e3donline/ToolChanger/Revo Hemera XS Direct Tool/Mirrored Tool/STPs/Blower fan duct (M).STEP

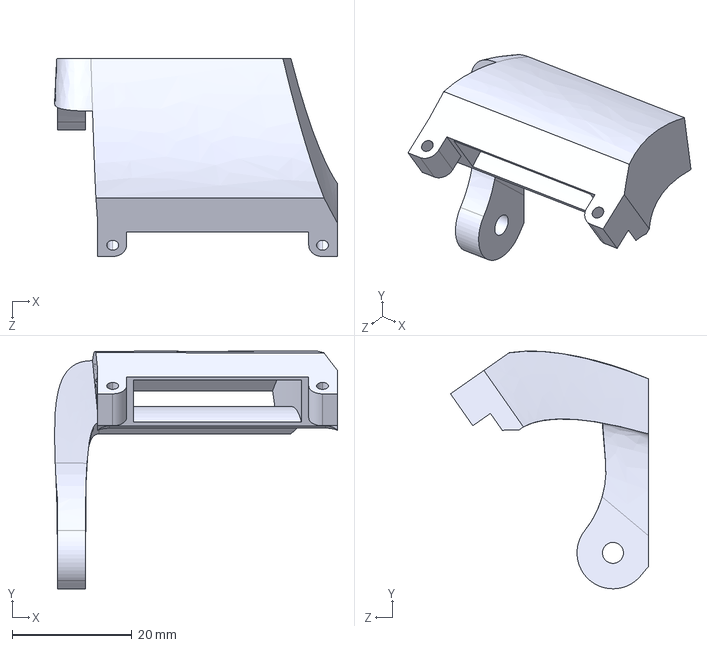
[picture p16: CAD file, 2023-03-06]
Revo Hemera XS Direct Tool/Mirrored Tool/STPs/Blower fan duct (M).STEP
47.2 x 39.6 x 33.0 mm
