e3donline/ToolChanger/Revo Hemera XS Direct Tool/Regular Tool/STPs/Dock brace.STEP

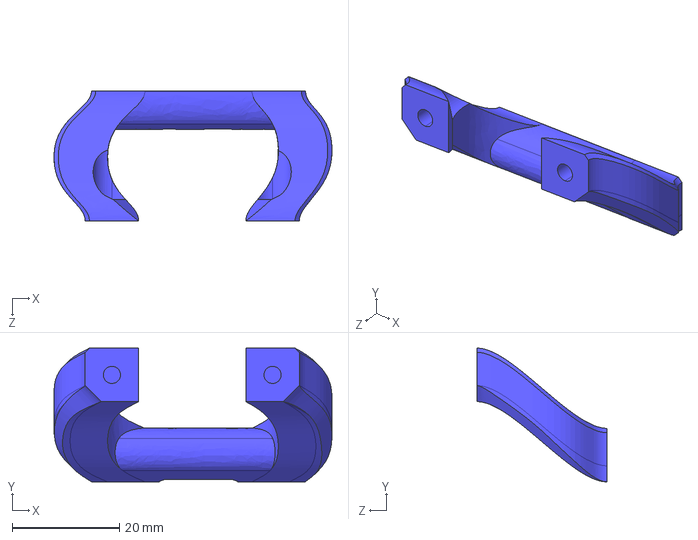
[picture p17: CAD file, 2023-03-06]
Revo Hemera XS Direct Tool/Regular Tool/STPs/Dock brace.STEP
51.9 x 25.0 x 24.3 mm
