e3donline/ToolChanger/STLs/Tool-Changer Cover Dot.stl

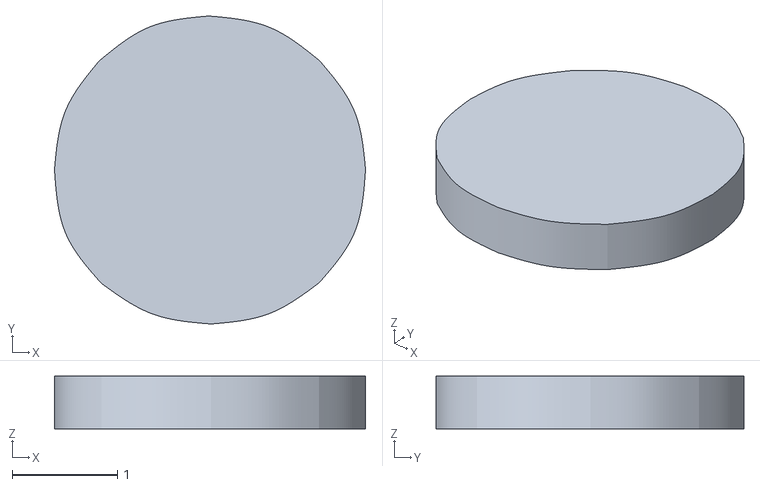
[picture p18: CAD file, 2019-06-24]
STLs/Tool-Changer Cover Dot.stl
2.95 x 2.92 x 0.5
