e3donline/ToolChanger/STPs/Tool-Changer Cover.step

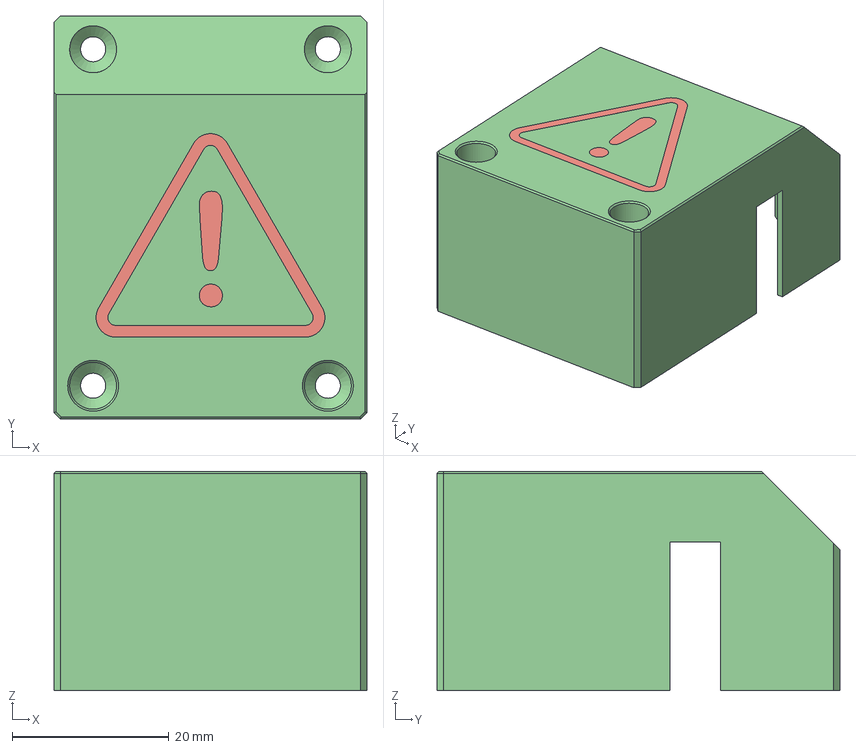
[picture p19: CAD file, 2019-07-31]
STPs/Tool-Changer Cover.step
40.0 x 51.5 x 28.0 mm
