e3donline/ToolChanger/Hemera Direct Tool/STPs/TC-DOCK-V6-DOCK-ADAPTER.step

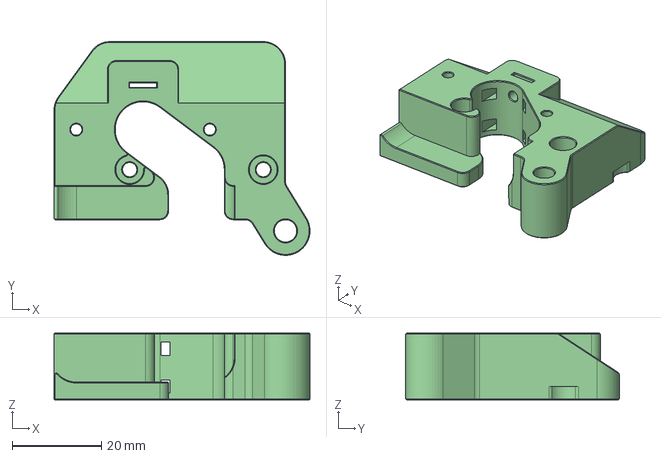
[picture p20: CAD file, 2021-03-15]
Hemera Direct Tool/STPs/TC-DOCK-V6-DOCK-ADAPTER.step
57.5 x 48.0 x 15.0 mm
