e3donline/ToolChanger/Revo Hemera XS Direct Tool/Regular Tool/STPs/Blower fan duct.STEP

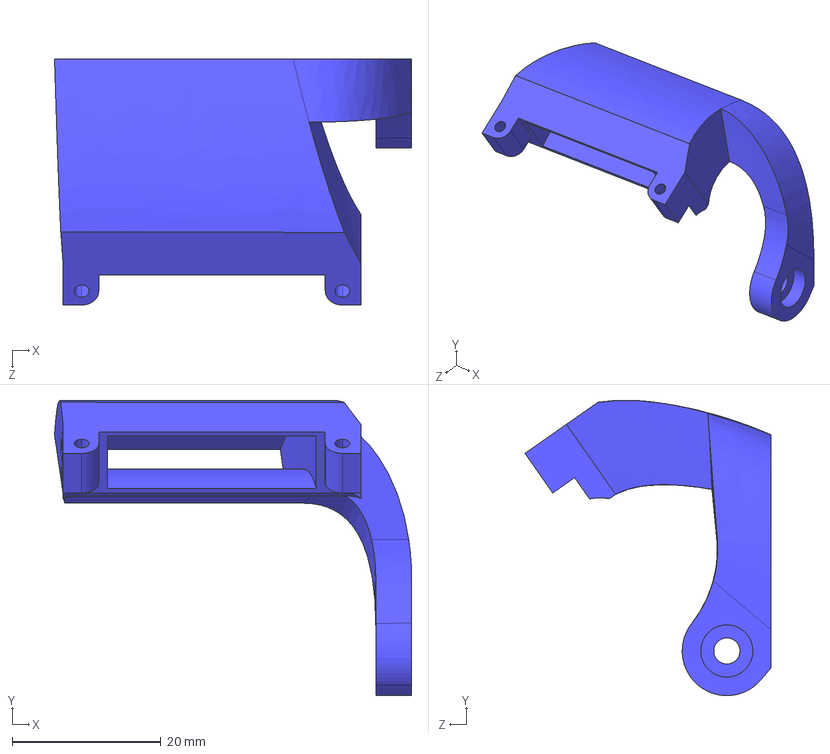
[picture p21: CAD file, 2023-03-06]
Revo Hemera XS Direct Tool/Regular Tool/STPs/Blower fan duct.STEP
47.9 x 39.6 x 33.0 mm
