e3donline/ToolChanger/STLs/X-Carriage Cables.stl

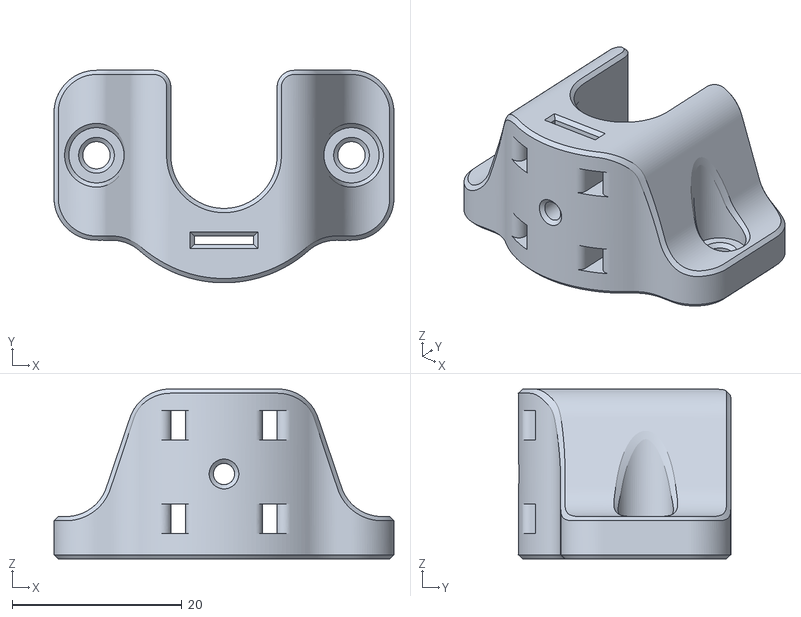
[picture p22: CAD file, 2019-06-24]
STLs/X-Carriage Cables.stl
40.0 x 25.0 x 20.0
