e3donline/ToolChanger/V6 Tool/STPs/V6 PCF Duct.step

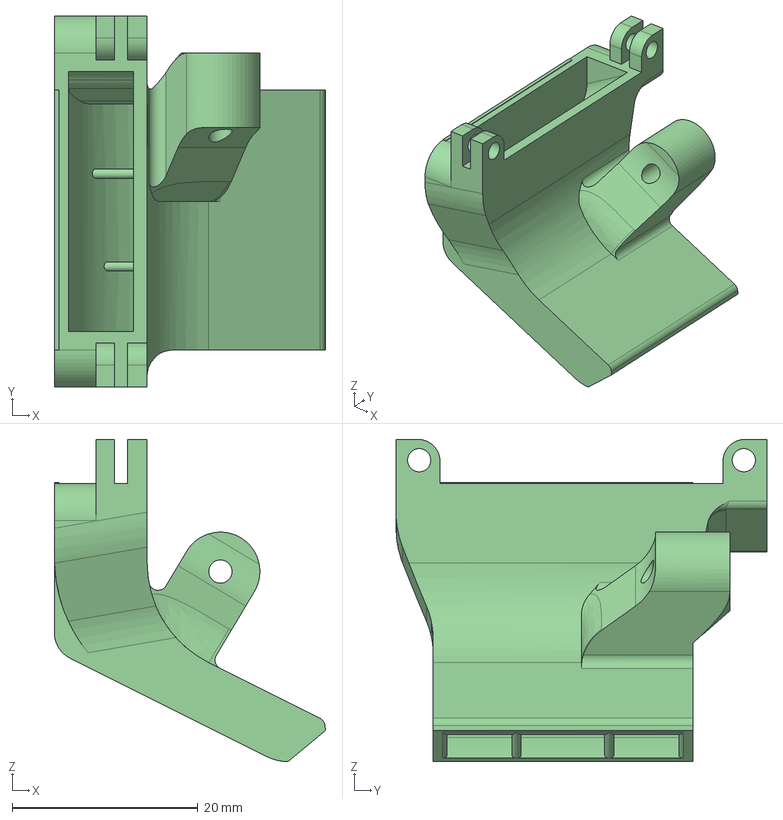
[picture p23: CAD file, 2019-07-31]
V6 Tool/STPs/V6 PCF Duct.step
29.2 x 40.0 x 34.8 mm
