e3donline/ToolChanger/Hemera Direct Tool/STPs/TC-V6-HEMERA-DOCK-BRACE-V2.step

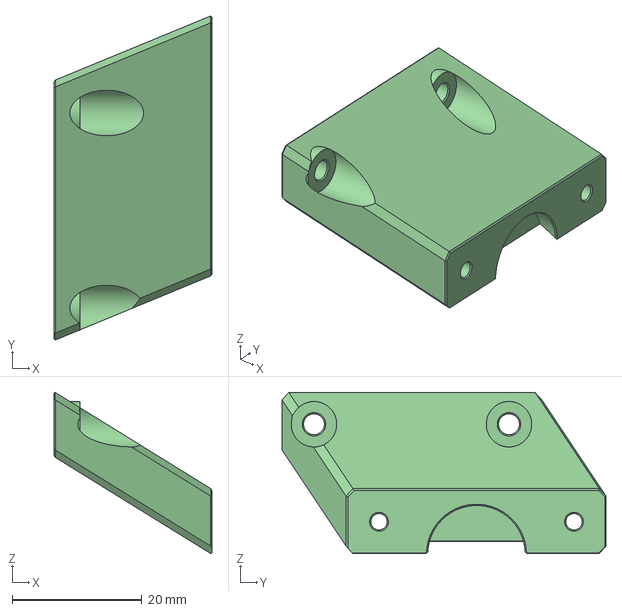
[picture p24: CAD file, 2021-03-15]
Hemera Direct Tool/STPs/TC-V6-HEMERA-DOCK-BRACE-V2.step
24.2 x 49.8 x 24.8 mm
