e3donline/ToolChanger/Revo Hemera XS Direct Tool/Mirrored Tool/STPs/Dock to RHXS (M).STEP

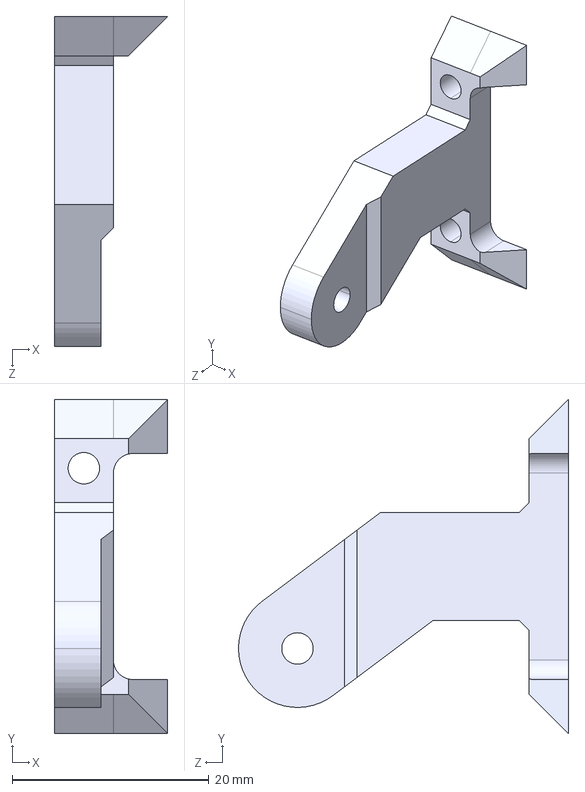
[picture p25: CAD file, 2023-03-06]
Revo Hemera XS Direct Tool/Mirrored Tool/STPs/Dock to RHXS (M).STEP
11.5 x 34.0 x 33.6 mm
