e3donline/ToolChanger/STLs/Tool-Changer Cover Triangle.stl

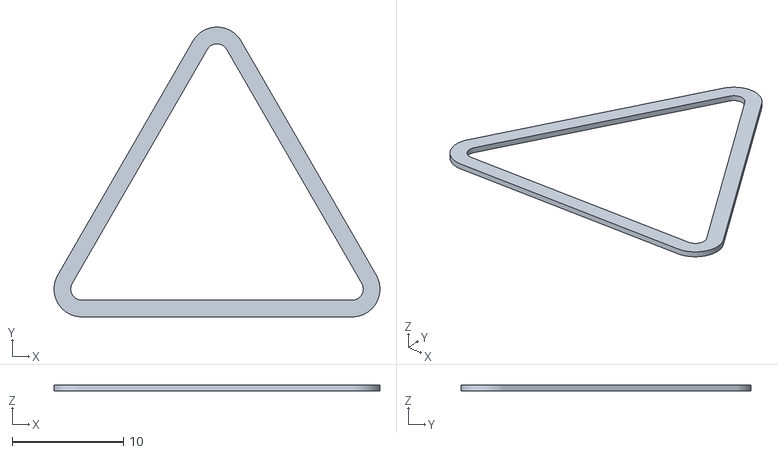
[picture p26: CAD file, 2019-06-24]
STLs/Tool-Changer Cover Triangle.stl
29.2 x 26.0 x 0.5
