e3donline/ToolChanger/STPs/TC-FACE 1.4.step

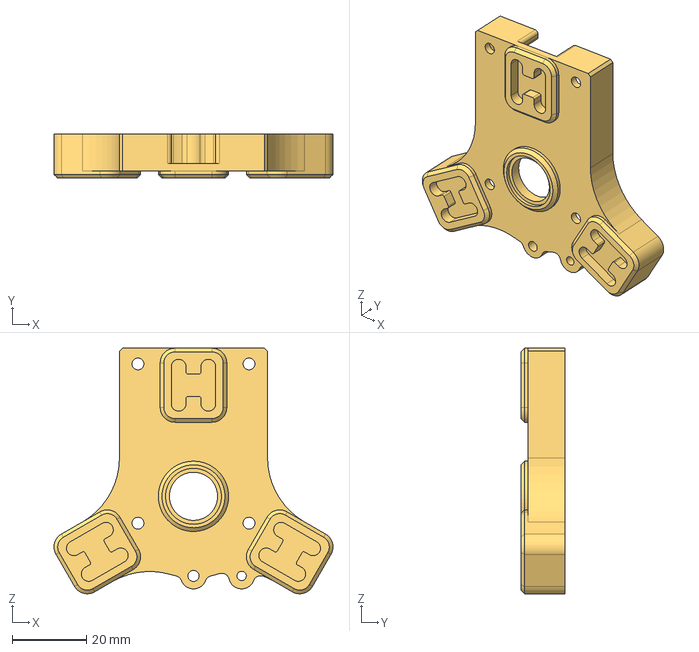
[picture p27: CAD file, 2019-06-25]
STPs/TC-FACE 1.4.step
75.4 x 12.0 x 66.3 mm
