e3donline/ToolChanger/V6 Tool/STPs/V6 PCF Fan Bracket.step

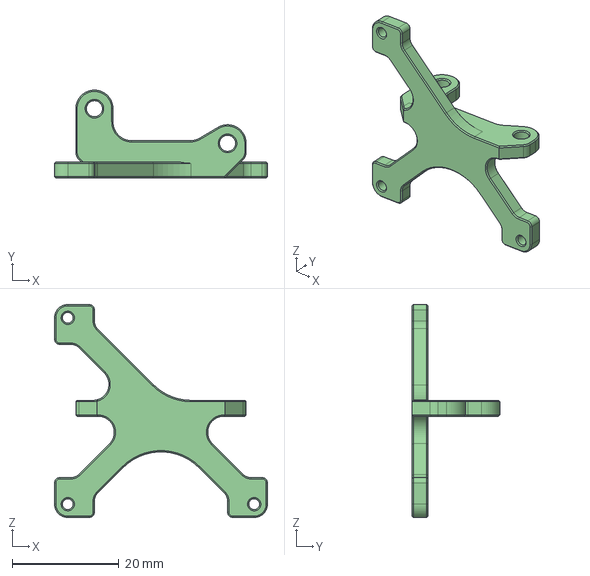
[picture p28: CAD file, 2019-07-31]
V6 Tool/STPs/V6 PCF Fan Bracket.step
40.0 x 16.5 x 40.0 mm
