e3donline/ToolChanger/Hemera Direct Tool/STPs/Hemera_PCF_Duct_-_V6.step

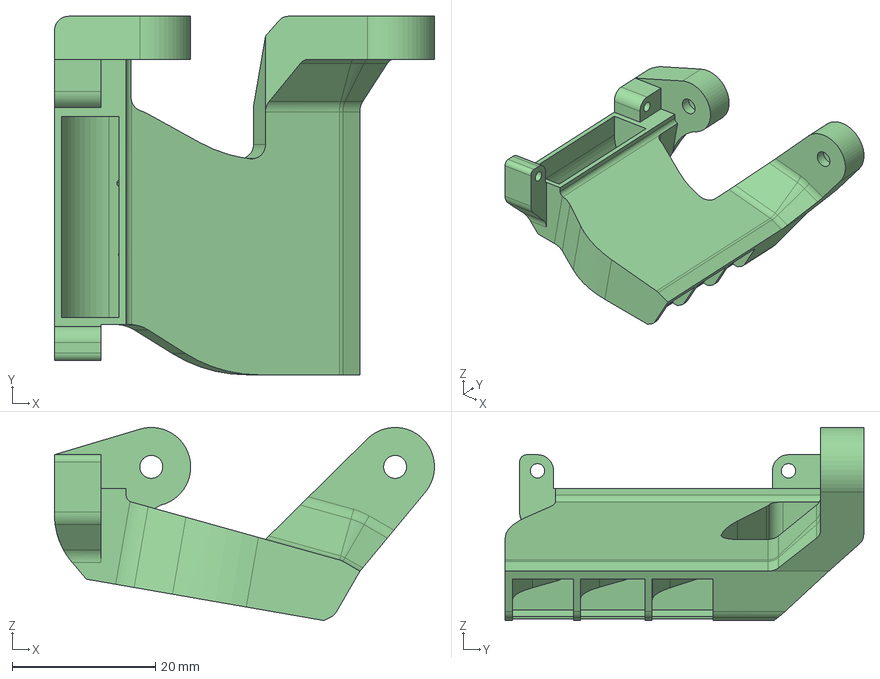
[picture p29: CAD file, 2021-03-15]
Hemera Direct Tool/STPs/Hemera_PCF_Duct_-_V6.step
53.0 x 50.0 x 26.9 mm
