e3donline/ToolChanger/Revo Hemera XS Direct Tool/Mirrored Tool/STPs/Toolplate to RHXS (M).STEP

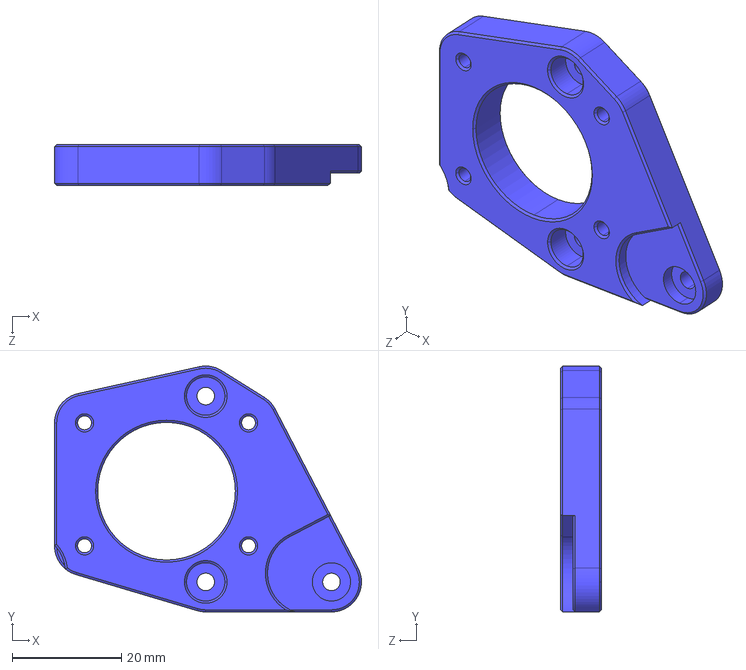
[picture p30: CAD file, 2023-03-06]
Revo Hemera XS Direct Tool/Mirrored Tool/STPs/Toolplate to RHXS (M).STEP
56.2 x 45.0 x 7.50 mm
