e3donline/ToolChanger/STPs/TC-MOD0.5-20T-SERVO-GEAR 1.5.step

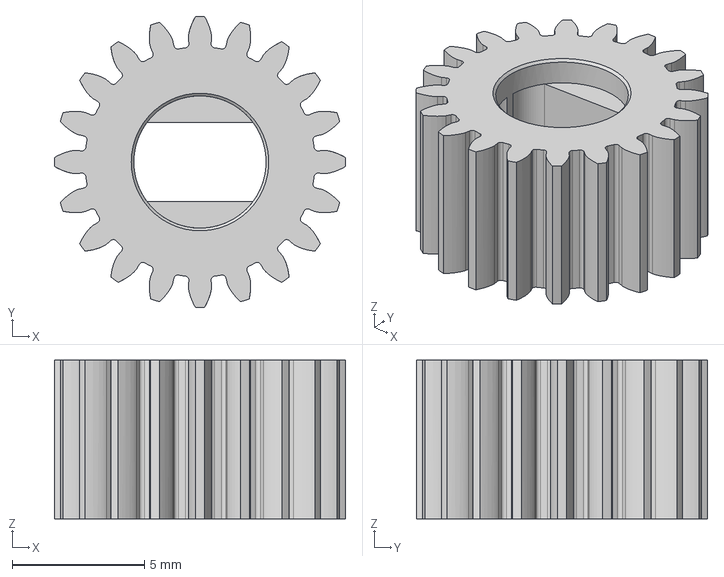
[picture p31: CAD file, 2019-06-24]
STPs/TC-MOD0.5-20T-SERVO-GEAR 1.5.step
11.0 x 11.0 x 6.00 mm
