e3donline/ToolChanger/V6 Tool/STPs/Volcano PCF Duct.step

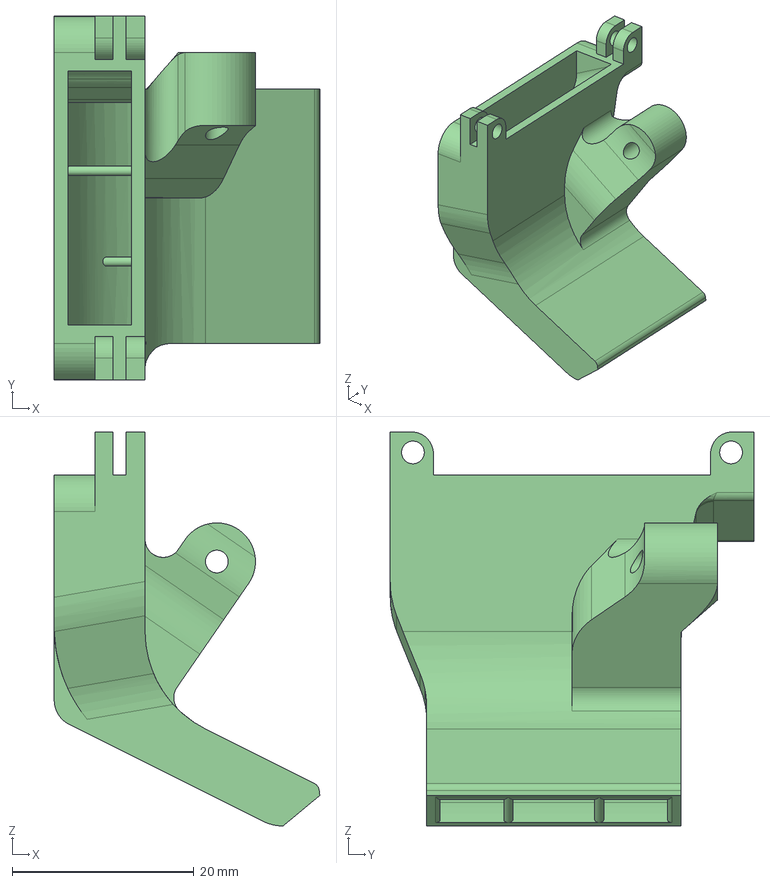
[picture p32: CAD file, 2019-07-31]
V6 Tool/STPs/Volcano PCF Duct.step
29.2 x 40.0 x 43.4 mm
