e3donline/ToolChanger/Hemera Direct Tool/STPs/TC-V6-DOCK-BRACKET-HEMERA-ADAPTER.step

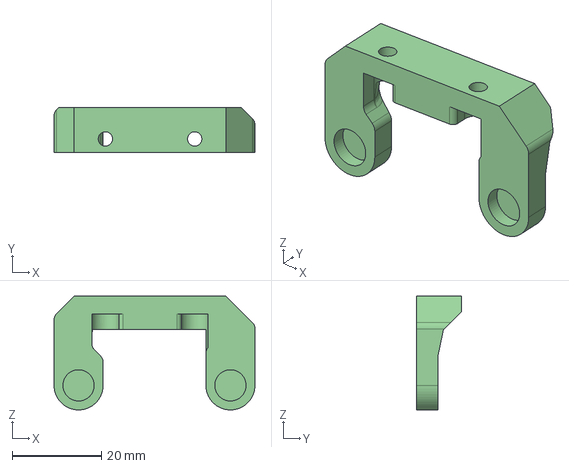
[picture p33: CAD file, 2021-03-15]
Hemera Direct Tool/STPs/TC-V6-DOCK-BRACKET-HEMERA-ADAPTER.step
45.0 x 10.0 x 25.5 mm
