e3donline/ToolChanger/STPs/TC-RAMP-6MM 1.3.step

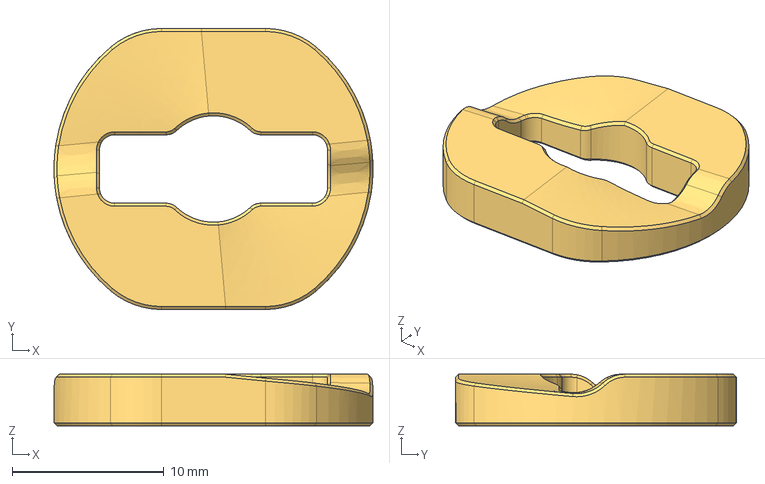
[picture p34: CAD file, 2019-06-24]
STPs/TC-RAMP-6MM 1.3.step
21.0 x 18.5 x 3.40 mm
