e3donline/ToolChanger/Hemera Direct Tool/STPs/TC-HEMERA-PLATE-ADAPTER.step

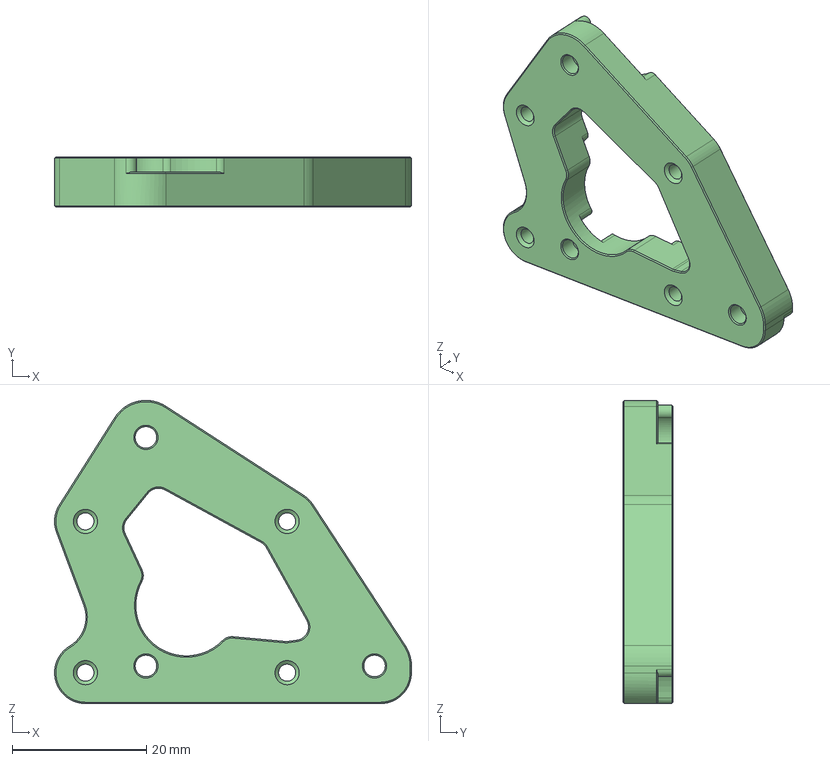
[picture p35: CAD file, 2021-03-15]
Hemera Direct Tool/STPs/TC-HEMERA-PLATE-ADAPTER.step
53.1 x 7.50 x 45.1 mm
