e3donline/ToolChanger/STPs/TC-MOTOR-BRACKET 1.0.step

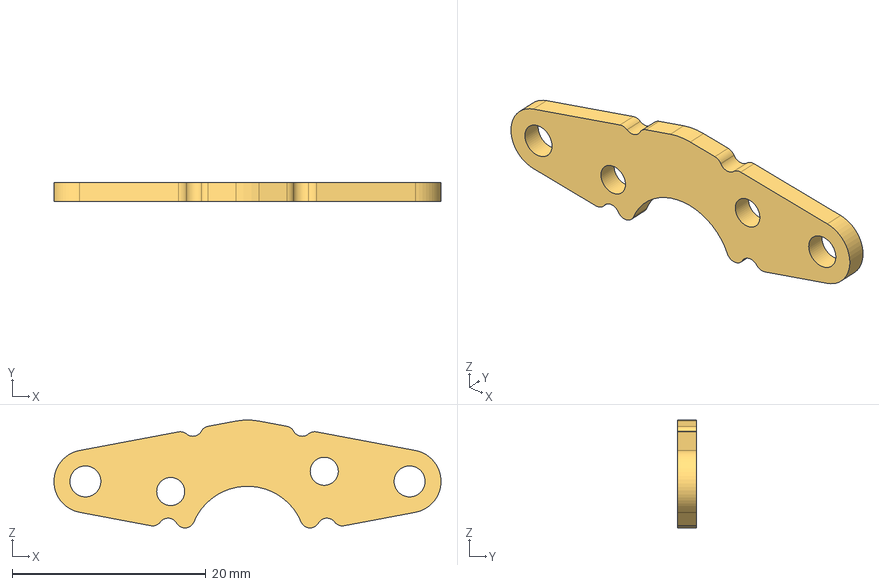
[picture p36: CAD file, 2019-06-24]
STPs/TC-MOTOR-BRACKET 1.0.step
40.0 x 2.00 x 11.1 mm
