e3donline/ToolChanger/V6 Tool/STPs/TC-HE-V6 1.1.step

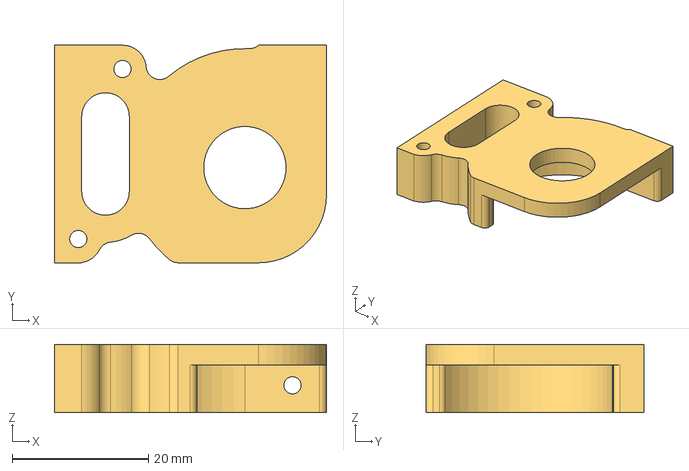
[picture p37: CAD file, 2019-06-24]
V6 Tool/STPs/TC-HE-V6 1.1.step
40.0 x 32.0 x 10.0 mm
