e3donline/ToolChanger/STPs/TC-MOD0.5-40T-GEAR 1.1.step

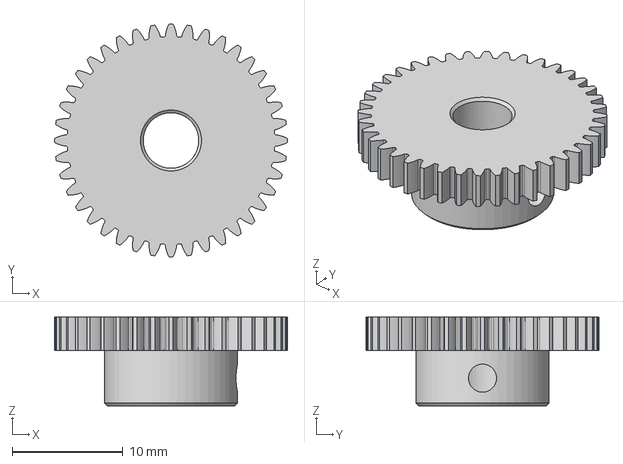
[picture p38: CAD file, 2019-06-24]
STPs/TC-MOD0.5-40T-GEAR 1.1.step
21.0 x 21.0 x 8.00 mm
