e3donline/ToolChanger/V6 Tool/STPs/TC-DOCK-V6 1.3.step

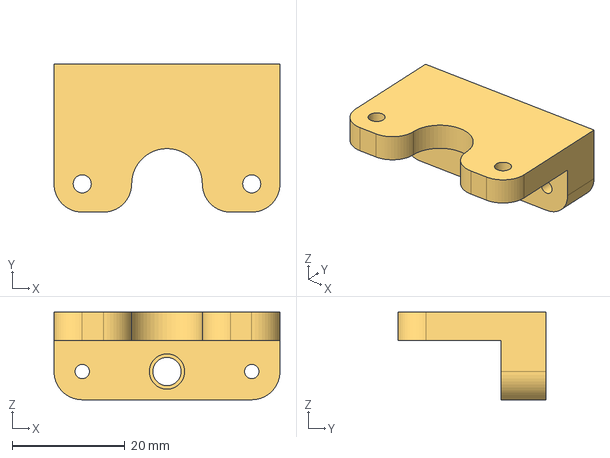
[picture p39: CAD file, 2019-06-24]
V6 Tool/STPs/TC-DOCK-V6 1.3.step
40.0 x 26.2 x 15.5 mm
