e3donline/ToolChanger/STPs/TC-PLATE v1.2.step

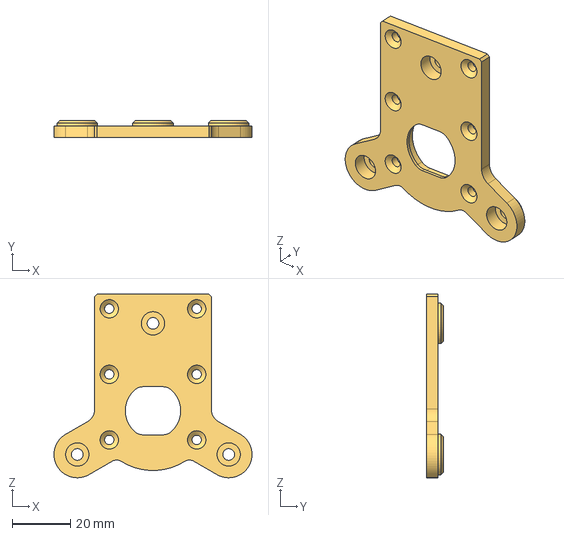
[picture p40: CAD file, 2019-06-24]
STPs/TC-PLATE v1.2.step
67.9 x 6.00 x 63.0 mm
