e3donline/ToolChanger/V6 Tool/STPs/TC-RECIEVER-V6 1.4.step

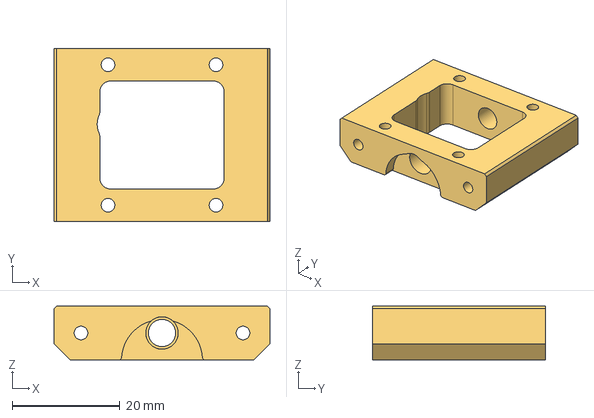
[picture p41: CAD file, 2019-06-24]
V6 Tool/STPs/TC-RECIEVER-V6 1.4.step
40.0 x 32.0 x 10.0 mm
