e3donline/ToolChanger/STPs/TC-SHAFT 1.5.step

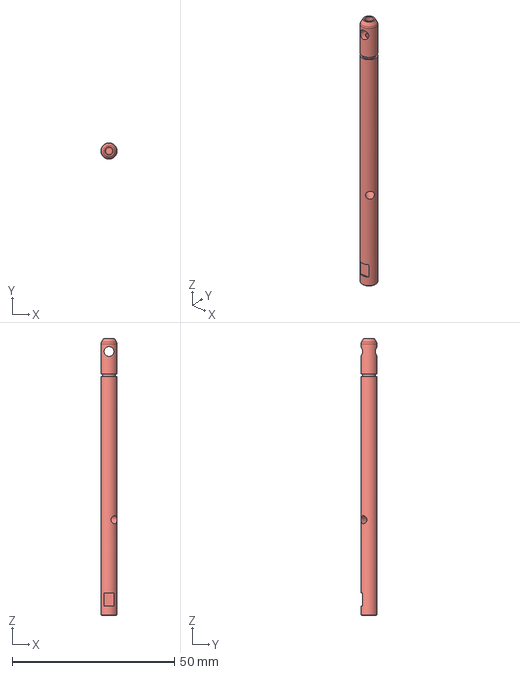
[picture p42: CAD file, 2019-06-24]
STPs/TC-SHAFT 1.5.step
5.00 x 5.00 x 85.2 mm
