e3donline/ToolChanger/V6 Tool/STPs/TC-DOCK-PIN-V6 1.1.step

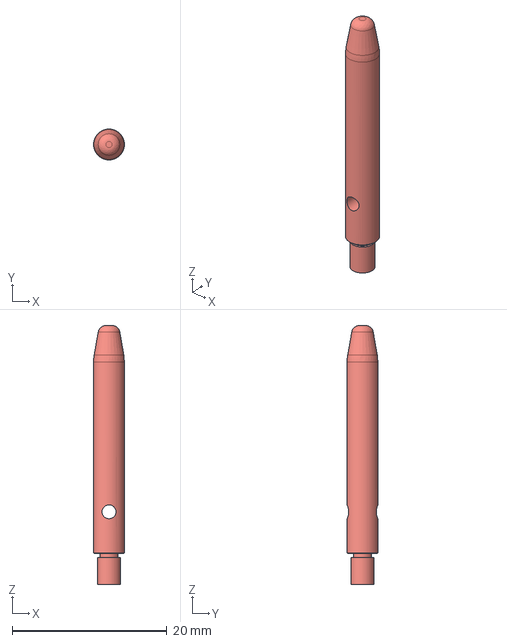
[picture p43: CAD file, 2019-06-24]
V6 Tool/STPs/TC-DOCK-PIN-V6 1.1.step
4.00 x 4.00 x 33.5 mm
