e3donline/ToolChanger/STPs/TC-BACK 1.3.step

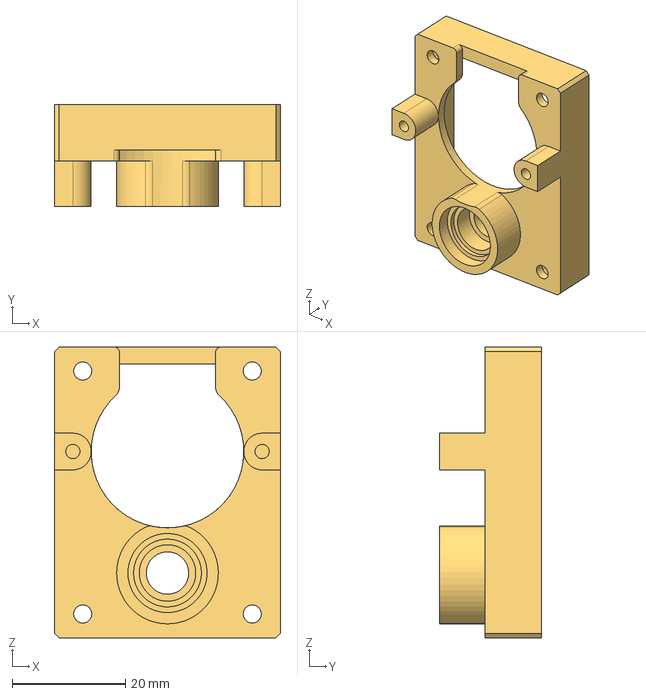
[picture p44: CAD file, 2019-06-24]
STPs/TC-BACK 1.3.step
40.0 x 18.0 x 51.5 mm
