e3donline/ToolChanger/V6 Tool/PDFs/TC-DOCK-PIN-V6 v1.1.pdf

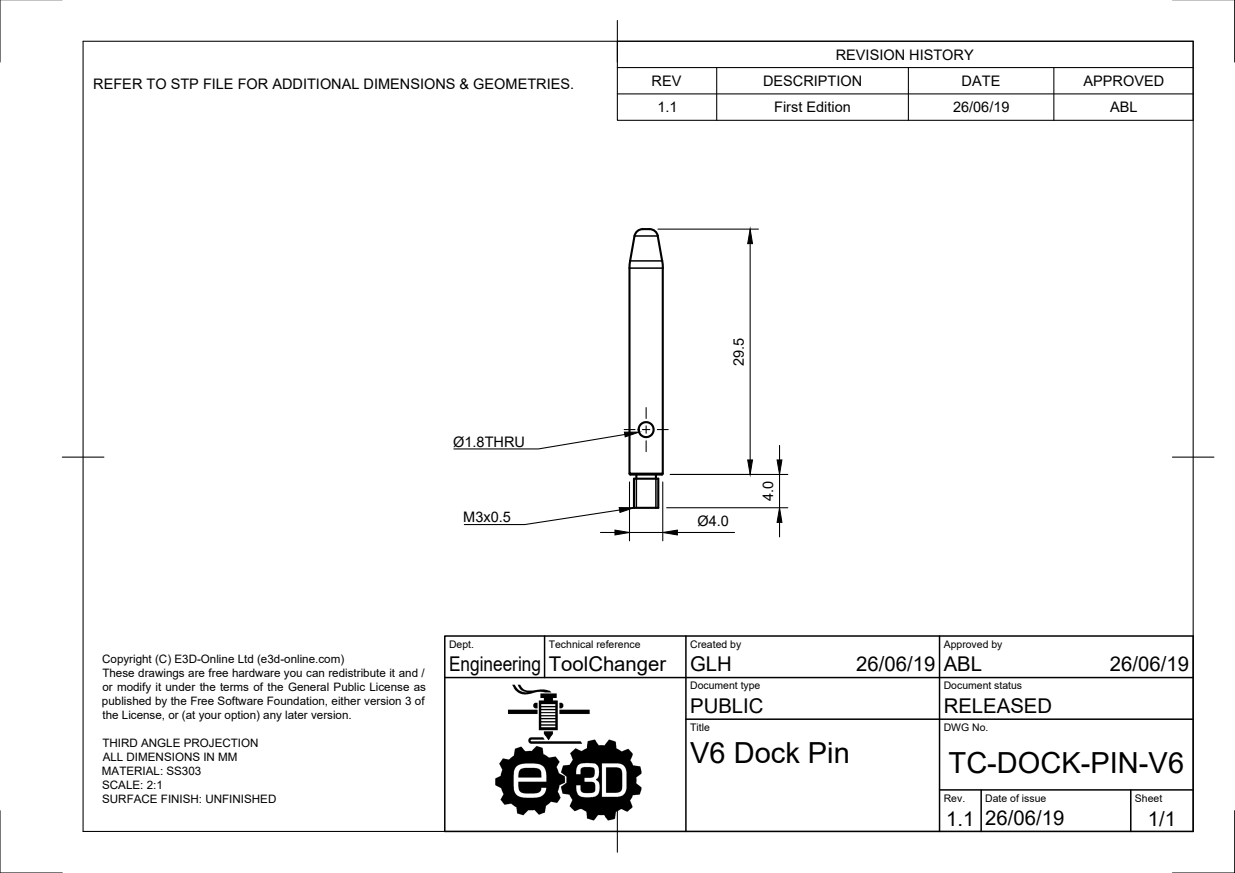
[picture p56: page 1]

REVISION HISTORY

REV | DESCRIPTION | DATE | APPROVED
1.1 | First Edition | 26/06/19 | ABL

REFER TO STP FILE FOR ADDITIONAL DIMENSIONS & GEOMETRIES.

Dept. Engineering | Technical reference ToolChanger | Created by GLH 26/06/19 | Approved by ABL 26/06/19

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

Document type PUBLIC | Document status RELEASED

the License, or (at your option) any later version.

Title | DWG No. TC-DOCK-PIN-V6 V6 Dock Pin

THIRD ANGLE PROJECTION
ALL DIMENSIONS IN MM
MATERIAL: SS303
SCALE: 2:1
SURFACE FINISH: UNFINISHED

Rev. 1.1 | Date of issue 26/06/19 | Sheet 1/1
