e3donline/ToolChanger/V6 Tool/PDFs/TC-HE-V6 v1.1.pdf

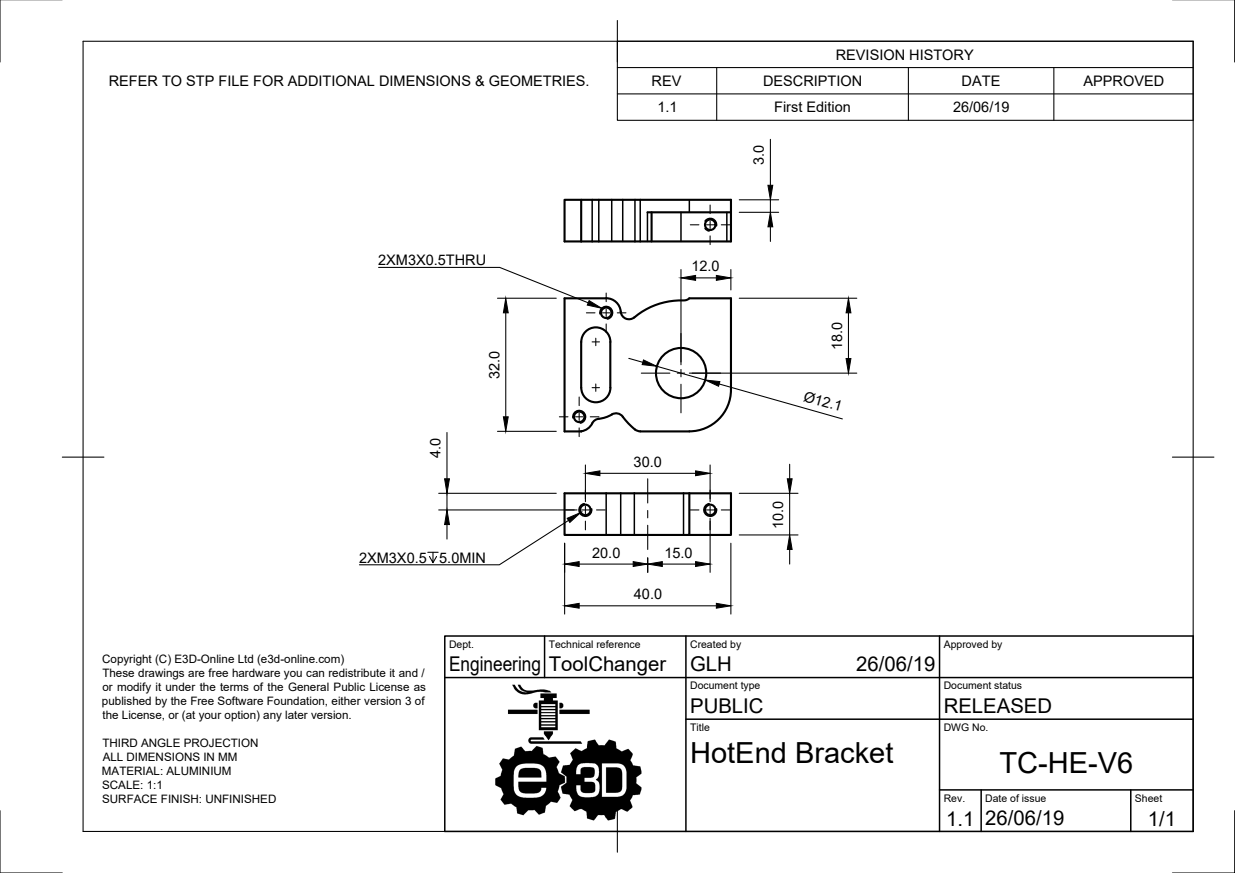
[picture p57: page 1]
15.0 2XM3X0.5 5.0MIN

REVISION HISTORY 12.0 2XM3X0.5THRU

REFER TO STP FILE FOR ADDITIONAL DIMENSIONS & GEOMETRIES.

REV | DESCRIPTION | DATE | APPROVED
1.1 | First Edition | 26/06/19

Dept. Engineering | Technical reference ToolChanger | Created by GLH 26/06/19 | Approved by

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

Document type PUBLIC | Document status RELEASED

the License, or (at your option) any later version.

Title HotEnd Bracket | DWG No. TC-HE-V6

THIRD ANGLE PROJECTION
ALL DIMENSIONS IN MM
MATERIAL: ALUMINIUM
SCALE: 1:1
SURFACE FINISH: UNFINISHED

Rev. 1.1 | Date of issue 26/06/19 | Sheet 1/1
